jorgeMartinez293/MimicRoboticHand/hardware/3d_models/images/9dd7e6e4-45f6-4609-a75b-79f62a137aab.png

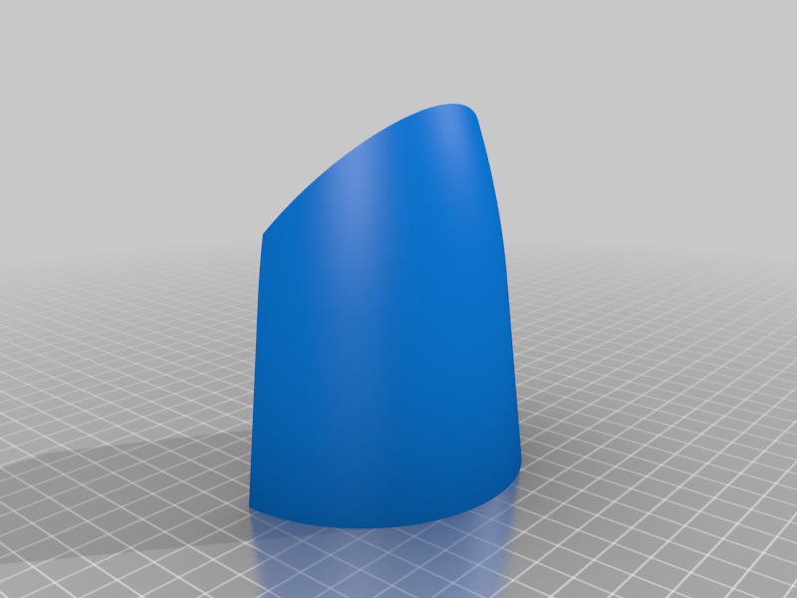
hardware/3d_models/images/9dd7e6e4-45f6-4609-a75b-79f62a137aab.png
